habworks/Arb_Power_Booster/TestResults/Neg_20V_Inrush_And_Discharge/Discharge.png

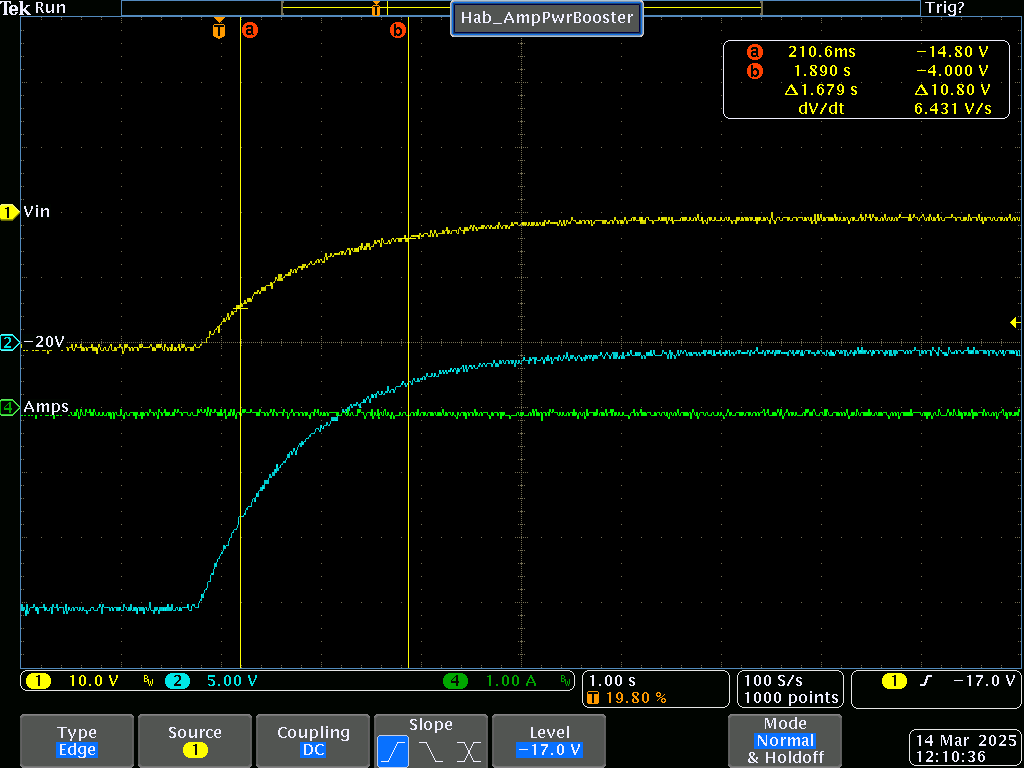
TestResults/Neg_20V_Inrush_And_Discharge/Discharge.png
