habworks/Arb_Power_Booster/TestResults/Neg_20V_Inrush_And_Discharge/Neg_20V_Inrush.png

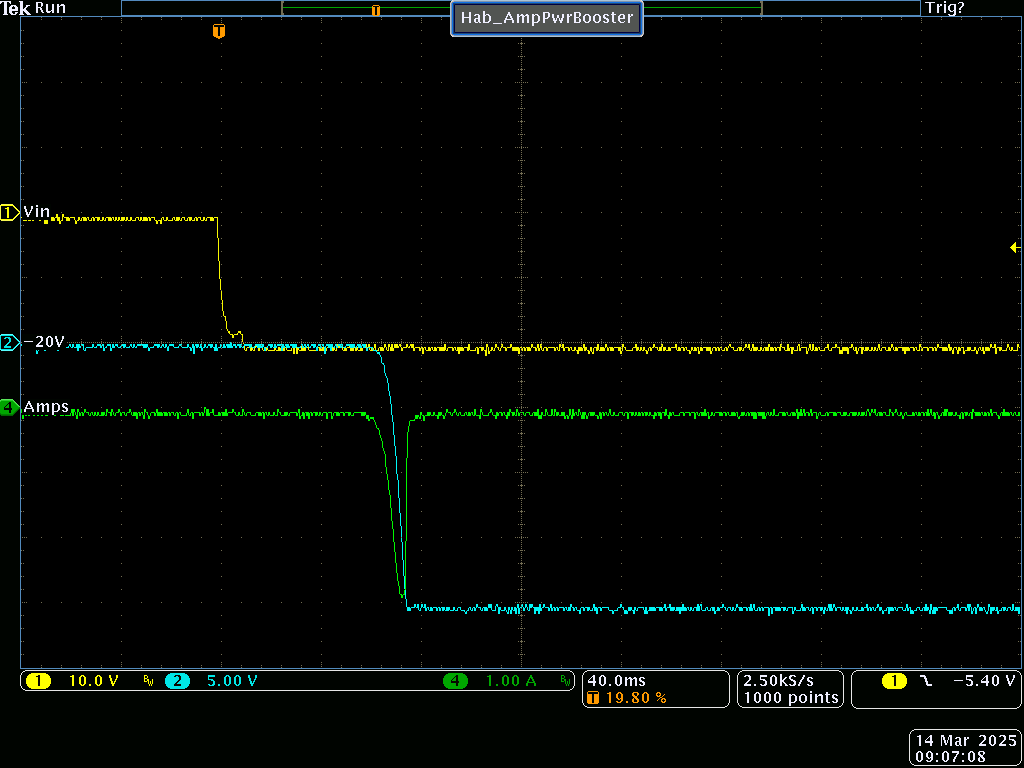
TestResults/Neg_20V_Inrush_And_Discharge/Neg_20V_Inrush.png
