habworks/Arb_Power_Booster/Simulate/Absolute_Value.asc

D1: diode; 1N4148
D2: diode; 1N4148
R1: res; 5K
R2: res; 10K
R3: res; 10K
R4: res; 10K
R5: res; 10K
R6: res; 10K
R7: res; 3K
R8: res; 4.99K
R9: res; 2.49K
U1: TLV9302
U3: TLV9302
V1: voltage; 15
V2: voltage; -15
V3: voltage; 10
Named nets: 0, VDD, VEE, VO, VIN, VO/2
.tran .010
