habworks/Arb_Power_Booster/Simulate/Current Amp-IC-Form-Single.asc

C1: cap; 300µF
C2: cap; .01µF
R1: res; 5
R2: res; 10
R3: res; .0065
R7: res; 10K
U1: OPA549
V1: voltage; -15V
V2: voltage; 15V
V3: voltage; SINE(9.5 .5 800 .001 0 0 10)
V4: voltage; 10
Named nets: 0, VS+, -VS, VIN, VO
.tran .003
