habworks/Arb_Power_Booster/Simulate/Current Amp-IC-Form-Dual.asc

C1: cap; 100µF
C2: cap; .01µF
R1: res; 3
R2: res; 10
R3: res; .1
R4: res; .1
R5: res; .001
R6: res; .001
R7: res; 10K
U1: OPA549
U2: OPA549
V1: voltage; -15V
V2: voltage; 15V
V3: voltage; SINE(10 1 5K .001 0 0 10)
Named nets: 0, VS+, -VS, VIN, VO
.tran .003
