habworks/Arb_Power_Booster/Simulate/NOT_USED_Current Amp-PowerAmp.asc

C1: cap; 100µ
D1: diode; 1N4148
D2: diode; 1N4148
D3: diode; 1N4148
Q1: npn; SST4401
Q2: pnp; SST4403
Q3: pnp; SST4403
Q4: npn; 2SCR582D3
Q5: npn; 2SCR582D3
Q6: npn; 2SCR582D3
Q7: npn; SST4401
Q8: npn; 2SCR582D3
R1: res; 500
R2: res; 500
R3: res; .2
R4: res; .2
R5: res; 1K
R6: res; 3.3
R7: res; 10
R8: res; 1K
R9: res; 10K
R10: res; 10K
R11: res; .2
R12: res; .2
U1: TLV9351
V1: voltage; 15
V2: voltage; -15
V3: voltage; SINE(10 1 5k 1m 0 0 10)
V4: voltage; 3.3
Named nets: 0, VCC, VEE, VO, VI, VT, VB
.tran 10m
