habworks/Arb_Power_Booster/Simulate/Current Amplifier-1_REV_21.asc

CL: cap; 300µ
D7: schottky; 1N5817
D8: schottky; 1N5817
Q1: npn; 2SCR582D3
Q2: npn; 2N4401
Q3: pnp; DJT4030P
Q4: pnp; 2SAR582D3
Q5: npn; 2N4401
Q6: pnp; MMBT4403
Q7: pnp; 2SAR582D3
Q8: npn; 2N4401
Q9: pnp; 2SAR582D3
Q10: pnp; MMBT4403
Q11: npn; 2SCR582D3
Q12: pnp; MMBT4403
Q13: npn; 2SCR582D3
Q14: npn; 2N4401
Q15: npn; DJT4031N
Q16: pnp; 2SAR582D3
Q17: pnp; MMBT4403
Q18: npn; 2SCR582D3
R1: res; 200
R2: res; 510
R3: res; .1
R4: res; .1
R5: res; .1
R6: res; .1
R7: res; .1
R8: res; .1
R9: res; .1
R10: res; .1
R11: res; .01
R12: res; .01
R13: res; 10K
R14: res; 500
RL: res; 3
U1: TLV9351
V1: voltage; 16
V2: voltage; -16
V3: voltage; SINE(10 2 5K .0005 0 0 10); AC 15
V4: voltage; 15
Named nets: VCC, VEE, 0, VO, VIN, VB1, VB2
.tran 3m
;ac dec 3m 10 10K
Note emitter resistance of R1 is less than R2 because it was found if they were even the
negative output voltage swing would be less than the positive output swing - This provides more 
available base current for amplification.
Full test condition is input of 10KHz at sine wave of +/-15V peak to peak.  This will be unrealistic
in a real environment, but the circuit can support it with some loss of amplitude (hence BW).
.MODEL DJT4030P PNP (IS=5.5e-13 NF=1 ISE=1.3e-13 NE=1.5 BF=360 VAF=36 IKF=8 ISC=1.1e-13 NC=1.28 BR=55 VAR=6.6 IKR=1.4 RE=9e-3 RB=300e-3 RC=9e-3 CJE=380e-12 VJE=0.7 MJE=0.4 CJC=111e-12 VJC=0.4 MJC=0.35 TF=8.5e-10 TR=3.7e-9 XTB=1.6 QUASIMOD=1 RCO=0.24 GAMMA=6e-10)
.MODEL DJT4031N NPN (IS=1e-14 BF=200 VAF=100 IKF=0.3 XTB=1.5 BR=5 CJC=10pF CJE=20pF TF=0.5ns TR=10ns)
