habworks/Arb_Power_Booster/Simulate/Current_Inrush_Limiter.asc

C1: cap; 10µ
C2: cap; 1000µ
C3: cap; 10µ
C4: cap; 1000µ
R1: res; 20K
R2: res; 58K
R3: res; 10K
R4: res; 20K
R5: res; 47K
R6: res; 10K
R7: res; 10K
R8: res; 1.236K
R9: res; 10K
R10: res; 1K
R11: res; 2.1K
U1: MMSZ5239BS
U2: DMP6050SPS-13
U3: MMSZ5239BS
U4: DMNH6042SPDQ-13
U5: DMNH6042SPDQ-13
U6: TLV9351
U7: BZT52C2V0S
U8: DMP6050SPS-13
V1: voltage; PULSE(0 20 10e-3 1e-5 1e-5 .5 1 2)
V2: voltage; PULSE(0 20 10e-3 1e-5 1e-5 .5 1 2)
V3: voltage; 20V
V4: voltage; -20V
V5: voltage; -30
Named nets: 0, VIN+, VO+, VG_A, VIN-, VO-, VG_B, VCC, VDD, VO
.tran 500E-3
Current inrush limiter. Works with zener or resistor R1 in circuit.  
 
When using Zener diode clamps the VGS so as not to exceed the max VGS of the PMOS
When using R1 the VGs limit is set by voltage divider of R1 and R2
 
In either case the C1 and R2 work to slow the turn on of the PMOSFET
Circuit also has the benefit of reverse voltage connection because of the PMOSFET body diode
OPTIONAL: You can cascade the MOSFET to reduce 
the total power (and in rush) they have to consume
OPTIONAL: You can cascade the MOSFET to reduce 
the total power (and in rush) they have to consume
