habworks/Arb_Power_Booster/Simulate/LeakageCurren_PosVoltageMonitor.asc

R1: res; 10K
R2: res; 1.24K
U3: MMSZ5226BS
V1: voltage; 20
Named nets: 0, Vo
.tran 1
