habworks/Arb_Power_Booster/Simulate/Signal_SSR_Switched_REV_2.asc

D1: LED
M1: nmos; 2N7002
R1: res; 10K
R2: res; 10K
R3: res; 1K
R4: res; 3K
R5: res; 8K
R6: res; 10K
U1: MMSZ5239BS
U2: IRLML5103TRPBF
U3: BZX84C3V6W-7-F
V1: voltage; 16
V2: voltage; -16
Named nets: 0, VDD, VSS
.tran 1
