habworks/Arb_Power_Booster/Simulate/NOT_USED_Add_Back_In_Vbe_Offset.asc

C1: cap; 1µF
Q1: npn; 2N3904
Q2: pnp; 2N3906
Q3: npn; 2N3904
Q4: pnp; 2N3906
R1: res; 20K
R2: res; 20K
R3: res; 5K
R4: res; 10K
R5: res; 10K
R6: res; 10K
R7: res; 10K
R8: res; 10K
R9: res; 10K
R10: res; 5K
R11: res; 10K
R12: res; 0
R13: res; 0
U1: TLV9351
U2: TLV9351
V1: voltage; 20V
V2: voltage; -20V
V3: voltage; SINE(10 5 1K .002 0 0 5)
Named nets: 0, V+, V-, VBE, VO, VI, SIG
.tran 9e-3
