habworks/Arb_Power_Booster/Simulate/Voltage_Monitor.asc

D1: diode; 1N4148
D2: diode; 1N4148
R1: res; 10K
R2: res; 1.236K
R7: res; 10K
R8: res; 1.236K
R9: res; 10K
R10: res; 1K
R11: res; 2.1K
U1: BZT52C2V0S
U2: BZX84C3V6W-7-F
U6: TLV9351
V1: voltage; 30V
V3: voltage; 20V
V4: voltage; -20V
V5: voltage; -30V
Named nets: 0, VCC, VDD, VO-, VO+
.tran .1
Creates a ration of 0.110 of input voltage - Max allowable +input of 30V to max output of 3.3V
Creates a ration of -0.110 of input voltage - Max allowable -input of -30V to max output of +3.3V
Supply rails +/-20V
See notes on circuit calculation
