habworks/Arb_Power_Booster/Simulate/NOT_USED_Current Amp-Adj_Bias-Servo-1.asc

C1: cap; 1µ
C2: cap; 300µ
C6: cap; 1µ
J1: njf; 2N5484
Q1: npn; 2SCR582D3
Q2: npn; 2SCR582D3
Q3: pnp; 2SAR582D3
Q4: pnp; 2SAR582D3
Q7: npn; 2SCR582D3
Q8: npn; 2N3904
Q9: npn; 2N3904
Q10: npn; 2N3904
Q11: pnp; 2N3906
Q12: pnp; 2N3906
Q13: pnp; 2N3906
Q14: pnp; 2SAR582D3
Q15: npn; 2N2219A
Q16: pnp; 2N2907
R1: res; .1
R2: res; .1
R3: res; 47K
R4: res; 1
R5: res; 1K
R6: res; 1
R7: res; 1
R8: res; 1
R9: res; 1K
R10: res; 1
R11: res; 1
R12: res; 39
R18: res; 62
R19: res; 150
R20: res; 150
R21: res; 62
R22: res; 68
R23: res; 68
R24: res; .1
R25: res; .1
R26: res; 1
R27: res; 1
R28: res; 100
R29: res; 3
R30: res; 100
R31: res; 100
R32: res; .1
R33: res; .1
R34: res; 100K
R35: res; 100K
U2: LT1368
V1: voltage; SINE(0 15 4.7K 1m 0 0 10)
V4: voltage; 20
V5: voltage; 20
V6: voltage; 15
V7: voltage; 15
Named nets: 0, +V, -V, +15V, -15V, VIN, VO
.tran 3m
