habworks/Arb_Power_Booster/Firmware/ArbPwrBooster_App/STM32CubeIDE/Application/User/App_Support/Src/PID_Controller.c

/******************************************************************************************************
 * @file 			PID_Controller.c
 * @brief			Proportional-Integral-Derivative (PID) controller functions
 * ****************************************************************************************************
 * @author original Hab Collector (habco)\n
 *
 * @version         See Main_Support.h: FW_MAJOR_REV, FW_MINOR_REV, FW_TEST_REV
 *
 * @param Development_Environment \n
 * Hardware:        <STM32F764G-DISCO> \n
 * IDE:             STMCubeIDE VER 1.17.0 \n
 * Compiler:        GCC \n
 * Editor Settings: 1 Tab = 4 Spaces, Recommended Courier New 11
 *
 * @note            The associated header file provides MACRO functions for IO control
 *
 *                  This is an embedded application
 *                  It will be necessary to consult the reference documents to fully understand the code
 *                  It is suggested that the documents be reviewed in the order shown.
 *                    Schematic: IMR-005-SCH
 *                    STM32F746G_DISCO
 *                    IMR Engineering
 *
 * @copyright       IMR Engineering, LLC
 ********************************************************************************************************/

#include "PID_Controller.h"
#include "Main_Support.h"
#include <stdlib.h>


/********************************************************************************************************
* @brief Init of a PID struct for use.  Allocate the memory for use with the PID, assign the gains and set
* the init conditions
*
* @author original: Hab Collector \n
*
* @note: This memory is allocated and should never be freed
*
* @param Kp: Proportional Gain
* @param Ki: Integral Gain
* @param Kd: Derivative Gain
* @param MaxStepValue: Digital Pot reset value in steps see MCP45HVX1 driver
*
* @return: Pointer to the PID Controller structure
*
* STEP 1: Allocate the memory
* STEP 2: Assign gain constants and init conditions
********************************************************************************************************/
Type_PID_Controller * Init_PID_Controller(float Kp, float Ki, float Kd, uint8_t MaxStepValue)
{
    // STEP 1: Allocate the memory
    Type_PID_Controller *PID = (Type_PID_Controller *)malloc(sizeof(Type_PID_Controller));
    if (PID == NULL)
        systemErrorHandler(__FILE__, __LINE__, 0, "Failed to allocate memory for PID");

    // STEP 2: Assign gain constants and init conditions
    PID->Enable = false;
    PID->ProportionalGain = Kp;
    PID->IntegralGain = Ki;
    PID->DerivativeGain = Kd;
    PID->PreviousError = 0;
    PID->Integral = 0;
    PID->Output = 0;
    PID->PotStep = 0;
    PID->MaxStepValue = MaxStepValue;

    return(PID);

} // END OF Init_PID_Controller



/********************************************************************************************************
* @brief Reseting of the PID values when not in use - By resetting the error when not in use, the error terms
* in particular the integral term does not grow unbounded.
*
* @author original: Hab Collector \n
*
* @param PID: PID Controller Handle
*
* STEP 1: PID_Reset
* ********************************************************************************************************/
void PID_Reset(Type_PID_Controller *PID_Controller)
{
    // STEP 1: PID_Reset
    PID_Controller->Enable = false;
    PID_Controller->Integral = 0;
    PID_Controller->PreviousError = 0;

} // END OF PID_Reset



/********************************************************************************************************
* @brief Update the digital pot to control the current set point.  The digital pot is a divider to the output
* signal.  When the current limit is surpassed, the digital pot is used to limit the output voltage.  By
* limiting the output voltage, the output current is reduced.  When the output voltage is reduced to the point
* the output current matches the current limit - this is in effect constant current mode.  The feedback loop
* encompasses the output current measure, the current limit, and the digital POT control.
*
* @author original: Hab Collector \n
*
* @note: This memory is allocated and should never be freed
*
* @param PID: PID Controller Handle
* @param MeasuredCurrent: Present current value
* @param CurrentLimit: current limit allowed
* @param DeltTime: Time between current samples
*
* @return: PID status
*
* STEP 1: Calculate the present error
* STEP 2: Calculate the Integral term
* STEP 3: Calculate the Derivative term
* STEP 4: Calculate the PID output (before conversion to digital pot units) by the sum of all errors
* STEP 5: Convert PID output to digital pot value
* STEP 6: Clamp PotValue within allowed range (0 to Total number of pot steps)
* STEP 7: Update digital pot step value - if step results in no attenuation reset the PID values
* ********************************************************************************************************/
Type_PID_Status PID_updateDigitalPot(Type_PID_Controller *PID, float MeasuredCurrent, float CurrentLimit, float DeltaTime)
{
    // STEP 1: Calculate the present error
    float PresentError = MeasuredCurrent - CurrentLimit;

    // STEP 2: Calculate the Integral term
    PID->Integral += PresentError * DeltaTime;

    // Optional: Integral anti-windup clamp (commented out, can be enabled if needed)
    // For now covered in step 7
//    if (PID->Integral > MaxIntegral)
//        PID->Integral = MaxIntegral;
//    else if (PID->Integral < 0.0f)
//        PID->Integral = 0.0f;

    // STEP 3: Calculate the Derivative term
    float Derivative = (PresentError - PID->PreviousError) / DeltaTime;
    PID->PreviousError = PresentError;

    // STEP 4: Calculate the PID output (before conversion to digital pot units) by the sum of all errors
    PID->Output = (PID->ProportionalGain * PresentError)
                + (PID->IntegralGain * PID->Integral)
                + (PID->DerivativeGain * Derivative);

    // STEP 5: Convert PID output to digital pot value
    int PotValue = (int)(PID->Output + 0.5f);   // Round to nearest integer
    PotValue = PID->MaxStepValue - PotValue;    // Must Invert Pot value: 0 = max attenuation, 255 = no attenuation

    // STEP 6: Clamp PotValue within allowed range (0 to Total number of pot steps)
    if (PotValue < 0)
    {
        PotValue = 0;
    }
    else if (PotValue > PID->MaxStepValue)
    {
        PotValue = PID->MaxStepValue;
    }
    // TODO: Hab test this MACRO - if good use it
    // PotValue = MIN_MAX_CLAMP(PotValue, 0, PID->MaxStepValue);

    // STEP 7: Update digital pot step value - if step results in no attenuation reset the PID values
    PID->PotStep = (uint8_t)PotValue;
    PID->Enable = (PID->PotStep == PID->MaxStepValue)? false:true;
    if (!PID->Enable)
        PID_Reset(PID);

    return(PID_UPDATE);

} // END OF PID_updateDigitalPot
