habworks/Arb_Power_Booster/Firmware/ArbPwrBooster_App/STM32CubeIDE/Application/User/App_Support/Src/ADC_Support.c

/** ****************************************************************************************************
 * @file            ADC_Support.c
 * @brief           A collection of functions relevant to the ADC peripheral channels and their conversions
 * ****************************************************************************************************
 * @author original Hab Collector (habco)\n
 *
 * @version         See Main_Support.h: FW_MAJOR_REV, FW_MINOR_REV, FW_TEST_REV
 *
 * @param Development_Environment \n
 * Hardware:        <STM32F764G-DISCO> \n
 * IDE:             STMCubeIDE VER 1.17.0 \n
 * Compiler:        GCC \n
 * Editor Settings: 1 Tab = 4 Spaces, Recommended Courier New 11
 *
 * @note            The associated header file provides MACRO functions for IO control
 *
 *                  This is an embedded application
 *                  It will be necessary to consult the reference documents to fully understand the code
 *                  It is suggested that the documents be reviewed in the order shown.
 *                    Schematic: IMR-005-SCH
 *                    STM32F746G_DISCO
 *                    IMR Engineering
 *
 * @copyright       IMR Engineering, LLC
 ********************************************************************************************************/

#include "ADC_Support.h"
#include "Main_Support.h"
#include "IO_Support.h"
#include "Terminal_Emulator_Support.h"
#include "MCP45HVX1_Driver.h"
#include "RMS_Calculate.h"
#include "PID_Controller.h"
#include "stm32f7xx_hal_adc.h"
#include "cmsis_os2.h"
#include <string.h>
#include <stdlib.h>
#include <stdio.h>
#include <math.h>


extern ADC_HandleTypeDef hadc1;
extern ADC_HandleTypeDef hadc3;

// Global
uint16_t ADC1_CountValue[ADC1_NUMBER_OF_CHANNELS];
uint16_t ADC3_CountValue[ADC3_NUMBER_OF_CHANNELS];
static double System_ADC_Reference = ADC_REFERENCE_VOLTAGE;     // Init condition - it will be updated later in calculation of ADC1 3V3

// Static Function Declarations
static Type_16b_FIFO *Init_FIFO_Buffer(uint16_t *Buffer, uint8_t BufferLength, uint16_t InitLoadValue);
static void writeTo_FIFO_Buffer(Type_16b_FIFO *Buffer, uint16_t Value);
static double calculateSystem_3V3(void);
static double calculateSystemTemp(void);
static double calculateSystemSupply(Type_16b_FIFO *FIFO_SupplyRail);
static void calculateChannelCurrent(double ADC_AmpMonitorCount, Type_16b_FIFO *FIFO_AmpMon, Type_ChannelConfig *Channel, Type_RMS *RMS_AmpMon);
static void calculateChannelVoltage(double ADC_VoltMonitorCount, Type_16b_FIFO *FIFO_VoltMon, Type_ChannelConfig *Channel, Type_RMS *RMS_VoltMon);

// Static FIFO Declarations
// System 3V3
static uint16_t BufferSystem_3V3[SYSTEM_3V3_BUFFER_SIZE] = {0x0000};
static Type_16b_FIFO *FIFO_System_3V3;
// System Temperature
static uint16_t BufferSystemTemp[SYSTEM_TEMP_BUFFER_SIZE] = {0x0000};
static Type_16b_FIFO *FIFO_SystemTemp;
// Positive VS Supply Rail Monitor
static uint16_t Buffer_PVS_Supply[SYSTEM_PVS_BUFFER_SIZE] = {0x0000};
static Type_16b_FIFO *FIFO_PVS_Supply;
// Negative VS Supply Rail Monitor
static uint16_t Buffer_NVS_Supply[SYSTEM_NVS_BUFFER_SIZE] = {0x0000};
static Type_16b_FIFO *FIFO_NVS_Supply;
// CH1 Current Monitor
static uint16_t Buffer_CH1_AmpMon[CH1_AMP_MON_BUFFER_SIZE] = {0x0000};
static Type_16b_FIFO *FIFO_CH1_AmpMon;
// CH2 Current Monitor
static uint16_t Buffer_CH2_AmpMon[CH2_AMP_MON_BUFFER_SIZE] = {0x0000};
static Type_16b_FIFO *FIFO_CH2_AmpMon;
// CH1 Current Monitor
static uint16_t Buffer_CH1_VoltMon[CH1_VOLT_MON_BUFFER_SIZE] = {0x0000};
static Type_16b_FIFO *FIFO_CH1_VoltMon;
// CH2 Current Monitor
static uint16_t Buffer_CH2_VoltMon[CH2_VOLT_MON_BUFFER_SIZE] = {0x0000};
static Type_16b_FIFO *FIFO_CH2_VoltMon;

// Static RMS Struct Declarations
static float CH1_AmpMonBuffer[RMS_WINDOW_SIZE];
static Type_RMS *RMS_CH1_AmpMon;
static float CH2_AmpMonBuffer[RMS_WINDOW_SIZE];
static Type_RMS *RMS_CH2_AmpMon;
static float CH1_VoltMonBuffer[RMS_WINDOW_SIZE];
static Type_RMS *RMS_CH1_VoltMon;
static float CH2_VoltMonBuffer[RMS_WINDOW_SIZE];
static Type_RMS *RMS_CH2_VoltMon;

// Static PID Controller Declarations
//static Type_PID_Controller *PID_CH1_DigitalPot;


/********************************************************************************************************
* @brief Init the ADC for ADC1 (2 channels) and ADC3 (3 channels).
* ADC1 handles:
*    Temperature
*    3.3V measurement
* ADC3 handles:
*    -VS Supply Rail
*    +VS Supply Rail
*    CH1 Current Monitor
*    CH2 Current Monitor
*    CH1 Voltage Monitor
*    CH2 Voltage Monitor
*
* @author original: Hab Collector \n
*
* @note: ADC1 is set in DMA single shot conversion mode - software start required for new conversion
* @note: ADC3 is set in DMA continuous conversion mode - continuous non-stop conversions once started
* @note: See the ADC DMA callback HAL_ADC_ConvCpltCallback
* @note: The STM32F series makes no provision for a calibration as it is trimmed by the factory
* @note: See function ADC13_StartConversion() - which actually starts the conversion
* @note: See also ArbPwrBooster member Ready
*
* STEP 1: Enable Internal reference and temperature measure
* STEP 2: Init FIFO Buffers for use with ADC1: Micro-Temp Sensor, System 3.3V
* STEP 3: Init FIFO Buffers for use with ADC3: ±VS rail, CH1 & CH2 Amp Monitor
* STEP 4: Init RMS structures
* STEP 5: Init PID structures
********************************************************************************************************/
void Init_ADC_Hardware(void)
{
    // STEP 1: Enable Internal reference and temperature measure
    ADC->CCR |= ADC_CCR_TSVREFE_Msk;

    // STEP 2: Init FIFO Buffers for use with ADC1: Micro-Temp Sensor, System 3.3V
    FIFO_SystemTemp = Init_FIFO_Buffer(BufferSystemTemp, SYSTEM_TEMP_BUFFER_SIZE, 0);
    FIFO_System_3V3 = Init_FIFO_Buffer(BufferSystem_3V3, SYSTEM_3V3_BUFFER_SIZE, ADC_REF_VOLTAGE_COUNT);

    // STEP 3: Init FIFO Buffers for use with ADC3: ±VS rail, CH1 & CH2 Amp Monitor
    FIFO_NVS_Supply = Init_FIFO_Buffer(Buffer_NVS_Supply, SYSTEM_NVS_BUFFER_SIZE, 0);
    FIFO_PVS_Supply = Init_FIFO_Buffer(Buffer_PVS_Supply, SYSTEM_PVS_BUFFER_SIZE, 0);
    FIFO_CH1_AmpMon = Init_FIFO_Buffer(Buffer_CH1_AmpMon, CH1_AMP_MON_BUFFER_SIZE, 0);
    FIFO_CH2_AmpMon = Init_FIFO_Buffer(Buffer_CH2_AmpMon, CH2_AMP_MON_BUFFER_SIZE, 0);
    FIFO_CH1_VoltMon = Init_FIFO_Buffer(Buffer_CH1_VoltMon, CH1_VOLT_MON_BUFFER_SIZE, 0);
    FIFO_CH2_VoltMon = Init_FIFO_Buffer(Buffer_CH2_VoltMon, CH2_VOLT_MON_BUFFER_SIZE, 0);

    // STEP 4: Init RMS structures
    RMS_CH1_AmpMon = Init_RMS_Class(CH1_AmpMonBuffer, RMS_WINDOW_SIZE);
    RMS_CH2_AmpMon = Init_RMS_Class(CH2_AmpMonBuffer, RMS_WINDOW_SIZE);
    RMS_CH1_VoltMon = Init_RMS_Class(CH1_VoltMonBuffer, RMS_WINDOW_SIZE);
    RMS_CH2_VoltMon = Init_RMS_Class(CH2_VoltMonBuffer, RMS_WINDOW_SIZE);

    // STEP 5: Init PID structures
    ArbPwrBooster.CH1.PID = Init_PID_Controller(PID_Pk, PID_Pi, PID_Pd, MCP45HVX1_POT_FULL_RESOLUTION);
    ArbPwrBooster.CH2.PID = Init_PID_Controller(PID_Pk, PID_Pi, PID_Pd, MCP45HVX1_POT_FULL_RESOLUTION);

} // END OF Init_ADC_Hardware



/********************************************************************************************************
* @brief Start Conversions for both ADC1 and ADC3.  Note this function should be call only once as part of
* the start up process.  Though ADC1 is configured in single shot mode and the start can be called on the
* completion of every ADC1 conversion, ADC3 is configured in circular mode and does not (should not) be called
* repeatedly as the conversions will automatically restart.
*
* @author original: Hab Collector \n
*
* @note: ADC1 is configured in single shot mode and its conversion rate is based on the rate at which it is called
* @note: ADC3 is configured in circular mode and will automatically restart the conversions
*
* STEP 1: Start ADC 1 & ADC 3 conversion all channels
********************************************************************************************************/
void ADC13_StartConversion(void)
{
    HAL_StatusTypeDef ADC_InitStatus = HAL_OK;

    // STEP 1: Start ADC 1 & ADC 3 conversion all channels
    ADC_InitStatus |= HAL_ADC_Start_DMA(&hadc1, (uint32_t *)ADC1_CountValue, ADC1_NUMBER_OF_CHANNELS);
    ADC_InitStatus |= HAL_ADC_Start_DMA(&hadc3, (uint32_t *)ADC3_CountValue, ADC3_NUMBER_OF_CHANNELS);
    if (ADC_InitStatus != HAL_OK)
        systemErrorHandler(__FILE__, __LINE__, 0, "Failed to init ADC peripheral");

} // END OF ADC13_StartConversion



/********************************************************************************************************
* @brief Redefinition of the weak callback function for ADC conversion complete.  ADC1 and ADC3 values
* have been acquired this function updates the corresponding FIFO buffers and calls a unique function that
* performs the channel conversion.  Within ADC3 an attempt is made to make a more accurate (calibrated) measure
* An ADC offset error and gain error are channel specific measurements that are made to improve the overall
* accuracy of the ADC count reading.  The offset error is measure in ADC counts when the input to the ADC channel
* is at GND - ideally it should be 0, but if not, this is how many counts the ADC is offset by and therefore
* must be subtracted out.  The gain error relates more to quantization effects of the ADC.  It is measured at the
* highest ADC input possible (System Reference Voltage if possible, but certainly as large as you can get)
* and its value should ideally be 4096 (12b ADC) (if input is System Reference Voltage) or the expected calculated
* value. The Gain Error (GE) is calculated as Measured / Expected - no gain error would be a value of 1.0
*
* The counter var VS_UpdateCount was added.  This callback routine really runs for too long.  Without the
* use of VS_UpdateCount the TouchGFX will crash.  VS_UpdateCount minimize the time time spent in this callback
* by mostly not updating the VS supply rails - which in fact will not be changing by much, nor is there an RMS
* associated calculation - just an average.  A value of 1000 is used for the delay but as little as 10 worked.
* It is balance between update speed of the VS supply rail mean and the smoothness of the TouchGFX operation.
*
* ADC1 handles:
*    Temperature
*    3.3V measurement
* ADC3 handles:
*    -VS Supply Rail
*    +VS Supply Rail
*    CH1 Current Monitor
*    CH2 Current Monitor
*    CH1 Voltage Monitor
*    CH2 Voltage Monitor
*
* ADC1 Configuration
* RANK  ADC_CH  Port    Cycles  Net Name
* 1     Temp    NA      480     NA - Internal to IC
* 2     Vref    NA      480     NA - Internal to IC
*
* ADC3 Configuration:
* RANK  ADC_CH  Port    Cycles  Net Name
* 1     IN6     PF8     144     -VS_MON
* 2     IN7     PF9     144     +VS-MON
* 3     IN0     PA0     144     IO_MON_1
* 4     IN8     PF10    144     IO_MON_2
* 5     IN4     PF6     144     VI_MON_2
* 6     IN5     PF7     144     VI_MON_1
*
* ADC uses PCLK2 (108MHz) with a divisor of 8
*
* @author original: Hab Collector \n
*
* @note: This is redefinition - this function is define weak in the HAL but implemented here
* @note: The Rate toggle outputs are used to verify ADC conversion rate.  Conversion rate is calculated as:
* PCLK2 / ADC_Clock_Presclar * Total Conversion Cycles For All ADC_Channels
* @note: ADC3 conversion time = 64.00us or 15.625KHz (This is the sampling frequency)
* @note: ADC1 conversion time = 71.11us but the sample rate is governed by mainUpdateTaskActions() / GUI_UPDATE_RATE
* @note: As the sampling frequency is 15.63KHz the max frequency of the input signal (nyquist) 7.813KHz
* @note: The sampling frequency was limited by the Touch GFX - As this computation must take place periodically and
* outside of a task, faster sampling frequencies (for example 20KHz) could not be sustained without crashing the TouchGFX
* That said there is some room to possibly tweak this a little higher.  If only the channel current is being
* calculated for RMS you can definitely run at 20KHz sampling.  However the 15.63KHz sample is adjusted for
* both channels current and voltage monitoring RMS.
*
* @param hadc: Pointer to the ADC handler (ADC1 or ADC3)
*
* STEP 1: ADC1 Conversions: Micro-Temp Sensor, System 3.3V
* STEP 2: ADC3 Conversions: ±VS rail, CH1 & CH2 Amp Monitor
********************************************************************************************************/
void HAL_ADC_ConvCpltCallback(ADC_HandleTypeDef *hadc)
{
    static uint16_t VS_UpdateCount = 0;

    // STEP 1: ADC1 Conversions: Micro-Temp Sensor, System 3.3V
    if (hadc == &hadc1)
    {
        // System Temperature: See section 15.10 of STM32F746 Reference Manual (RM0385)
        writeTo_FIFO_Buffer(FIFO_SystemTemp, ADC1_CountValue[RANK_1]);
        ArbPwrBooster.SystemMeasure.TempDegreeC = calculateSystemTemp();
        // System 3.3V
        writeTo_FIFO_Buffer(FIFO_System_3V3, ADC1_CountValue[RANK_2]);
        System_ADC_Reference = calculateSystem_3V3();
        ArbPwrBooster.SystemMeasure.VDD_VDREF = System_ADC_Reference;
        // Stop the one shot ADC - it must be started
        HAL_ADC_Stop_DMA(&hadc1);
        // Toggle at the end of conversion - for testing: ADC1 actual conversion rate versus calculated - using here ADC3_C_RATE_TOGGLE() must comment out its use in step 2
        // ADC3_C_RATE_TOGGLE();
    }

    // STEP 2: ADC3 Conversions: ±VS rail, CH1 & CH2 Amp Monitor, CH1 & CH2 Volt Monitor
    if (hadc == &hadc3)
    {
        double ADC3_ErrorCompensatedCount;
        VS_UpdateCount++;
        if (VS_UpdateCount == 1000) // 1000 Value found by trial but it worked with as little as 10
        {
            // -VS Supply Rail
            ADC3_ErrorCompensatedCount = ((double)ADC3_CountValue[RANK_1] - ADC_NVS_OFFSET_ERROR) / ADC_NVS_GAIN_ERROR;
            writeTo_FIFO_Buffer(FIFO_NVS_Supply, ADC3_ErrorCompensatedCount);
            ArbPwrBooster.SystemMeasure.Negative_VS = calculateSystemSupply(FIFO_NVS_Supply) * -1.0;
            // +VS Supply Rail
            ADC3_ErrorCompensatedCount = ((double)ADC3_CountValue[RANK_2] - ADC_PVS_OFFSET_ERROR) / ADC_PVS_GAIN_ERROR;
            writeTo_FIFO_Buffer(FIFO_PVS_Supply, ADC3_ErrorCompensatedCount);
            ArbPwrBooster.SystemMeasure.Positive_VS = calculateSystemSupply(FIFO_PVS_Supply);
            VS_UpdateCount = 0;
        }
        // Current Monitor CH1
        ADC3_ErrorCompensatedCount = ((double)ADC3_CountValue[RANK_3] - ADC_IMON1_OFFSET_ERROR) / ADC_IMON1_GAIN_ERROR;
        writeTo_FIFO_Buffer(FIFO_CH1_AmpMon, ADC3_ErrorCompensatedCount);
        calculateChannelCurrent(ADC3_ErrorCompensatedCount, FIFO_CH1_AmpMon, &ArbPwrBooster.CH1, RMS_CH1_AmpMon);
        // Current Monitor CH2
        ADC3_ErrorCompensatedCount = ((double)ADC3_CountValue[RANK_4] - ADC_IMON2_OFFSET_ERROR) / ADC_IMON2_GAIN_ERROR;
        writeTo_FIFO_Buffer(FIFO_CH2_AmpMon, ADC3_ErrorCompensatedCount);
        calculateChannelCurrent(ADC3_ErrorCompensatedCount, FIFO_CH2_AmpMon, &ArbPwrBooster.CH2, RMS_CH2_AmpMon);
        // Voltage Monitor CH1
        ADC3_ErrorCompensatedCount = ((double)ADC3_CountValue[RANK_6] - ADC_VMON1_OFFSET_ERROR) / ADC_VMON1_GAIN_ERROR;
        writeTo_FIFO_Buffer(FIFO_CH1_VoltMon, ADC3_ErrorCompensatedCount);
        calculateChannelVoltage(ADC3_ErrorCompensatedCount, FIFO_CH1_VoltMon, &ArbPwrBooster.CH1, RMS_CH1_VoltMon);
        // Voltage Monitor CH2
        ADC3_ErrorCompensatedCount = ((double)ADC3_CountValue[RANK_5] - ADC_VMON2_OFFSET_ERROR) / ADC_VMON2_GAIN_ERROR;
        writeTo_FIFO_Buffer(FIFO_CH2_VoltMon, ADC3_ErrorCompensatedCount);
        calculateChannelVoltage(ADC3_ErrorCompensatedCount, FIFO_CH2_VoltMon, &ArbPwrBooster.CH2, RMS_CH2_VoltMon);
        // Toggle at the end of conversion - for testing: ADC3 actual conversion rate versus calculated
        ADC3_C_RATE_TOGGLE();
    }

} // END OF HAL_ADC_ConvCpltCallback



/********************************************************************************************************
* @brief Init of a FIFO buffer for use.  The base memory location for the buffer is cleared and memory for
* type is allocated.  The buffer is init with the write position at index 0
*
* @author original: Hab Collector \n
*
* @note: The passed buffer must be of type uint16_t
* @note: This memory is allocated and should never be freed
* @note: Buffers used for the collection of data used in a rolling average
*
* @param Buffer: Pointer to memory that will hold the buffer
* @param BufferLength: The total number of uint16_t
* @param InitLoadValue: Init value of the buffer
*
* @return: Pointer to the FIFO buffer structure
*
* STEP 1: Set the buffer values to 0 and allocate memory for the struct pointer
* STEP 2: Assign buffer pointer, length and set write location to buffer index
* STEP 3: Load the buffer with the init value
********************************************************************************************************/
static Type_16b_FIFO *Init_FIFO_Buffer(uint16_t *Buffer, uint8_t BufferLength, uint16_t InitLoadValue)
{
    // STEP 1: Set the buffer values to 0 and allocate memory for the struct pointer
    memset(Buffer, 0x00, (sizeof(uint16_t) * BufferLength));
    Type_16b_FIFO *FIFO_16Bit = (Type_16b_FIFO *)malloc(sizeof(Type_16b_FIFO));
    if (FIFO_16Bit == NULL)
        systemErrorHandler(__FILE__, __LINE__, 0, "Failed to allocate memory for FIFO");

    // STEP 2: Assign buffer pointer, length and set write location to buffer index
    FIFO_16Bit->Buffer = Buffer;
    FIFO_16Bit->Depth = BufferLength;
    FIFO_16Bit->WritePointer = &Buffer[0];
    FIFO_16Bit->Sum = 0;
    FIFO_16Bit->FirstOverFlow = false;

    // STEP 3: Load the buffer with the init value
    for (uint8_t Index = 0; Index < BufferLength; Index++)
    {
        writeTo_FIFO_Buffer(FIFO_16Bit, InitLoadValue);
    }

    return(FIFO_16Bit);

} // END OF Init_FIFO_Buffer



/********************************************************************************************************
* @brief Write a value to the FIFO buffer.  The write pointer is advance automatically.  The write pointer
* will loop back to the index to avoid memory leak.  A sum is calculated by means of adding the newest and
* removing the previous value - quicker than incrementally summing buffer values externally.
*
* @author original: Hab Collector \n
*
* @note: See Init_FIFO_Buffer function for additional details
* @note: Sum and depth members can be used for a quick external calculation of mean
*
* @param FIFO: Pointer to the 16b FIFO
* @param NewValue: Value to be written into FIFO - replaces oldest value
*
* STEP 1: Calculate buffer sum
* STEP 2: Write Value to the present location
* STEP 3: Advance write pointer to next address - loop back when end of write locations reached
********************************************************************************************************/
static void writeTo_FIFO_Buffer(Type_16b_FIFO *FIFO, uint16_t NewValue)
{
    // STEP 1: Calculate buffer sum
    if (!FIFO->FirstOverFlow)
    {
        FIFO->Sum = FIFO->Sum + NewValue;
    }
    else
    {
        uint16_t LastValue = *FIFO->WritePointer;
        FIFO->Sum = FIFO->Sum + NewValue;
        FIFO->Sum = FIFO->Sum - LastValue;
    }

    // STEP 2: Write Value to the present location
    *FIFO->WritePointer = NewValue;

    // STEP 3: Advance write pointer to next address - loop back when end of write locations reached
    uint16_t *NewWritePointer = FIFO->WritePointer + 1;
    if (NewWritePointer >= (FIFO->Buffer + FIFO->Depth))
    {
        FIFO->WritePointer = FIFO->Buffer;
        FIFO->FirstOverFlow = true;
    }
    else
        FIFO->WritePointer = NewWritePointer;

} // END OF writeTo_FIFO_Buffer



/********************************************************************************************************
* @brief Calculate the SYSTEM 3V3 voltage using the internal reference.  Formula is:
*    VDD = (Factory_ReferenceCalibration * 3.3) / ADC_VrefInt
* The ADC_VrefInt is mean value of a FIFO buffer which is used to establish a filtered result
*
* @author original: Hab Collector \n
*
* @note: For the STM32F746G-DISCO The Vref and VDD are the same
* @note: SYSTEM refers to quantities that impact the entire device - CHANNEL impacts on CH1 or CH2
*
* @return System VREF value the actual value we do not presume it is 3.3V
*
* STEP 1: Write Value to the present location
* STEP 2: Advance write pointer to next address - loop back when end of write locations reached
********************************************************************************************************/
static double calculateSystem_3V3(void)
{
    // STEP 1: Calculate the mean of the ADC 3V3 counts
    double Mean_3V3_Count = 0.0;
    Mean_3V3_Count = (double)((double)FIFO_System_3V3->Sum / FIFO_System_3V3->Depth);

    // STEP 2: Using the mean value calculate the System 3V3
    uint16_t VRefInternalCal = *VREFINT_CAL_ADDR;
    double System_3V3 = (VRefInternalCal * ADC_REFERENCE_VOLTAGE) / Mean_3V3_Count;
    return(System_3V3);

} // END OF calculateSystem_3V3



/********************************************************************************************************
* @brief Calculate the SYSTEM temperature.  The formula is taken from See section 15.10 of STM32F746 Reference
* Manual (RM0385).  Makes uses of the filtered value for Vref (System_ADC_Reference).
*
* @author original: Hab Collector \n
*
* @note: For the STM32F746G-DISCO The Vref and VDD are the same
* @note: SYSTEM refers to quantities that impact the entire device - CHANNEL impacts on CH1 or CH2
* @note: According to the datasheet this is not going to be a very accurate absolute measure because of the
* temperature offset.  However it should be very good at making relative measurements to ±1.5C°.
*
* @return System Temperature in °C as measured by the STM32F746 uC.
*
* STEP 1: Calculate the mean of the ADC Temperature counts
* STEP 2: Using the mean value calculate the System Temperature in °C
********************************************************************************************************/
static double calculateSystemTemp(void)
{
    // STEP 1: Calculate the mean of the ADC Temperature counts
    double MeanTempCount = 0.0;
    MeanTempCount = (double)((double)FIFO_SystemTemp->Sum / FIFO_SystemTemp->Depth);

    // STEP 2: Using the mean value calculate the System Temperature in °C
    double VoltageTempSensor = (MeanTempCount * System_ADC_Reference) / ADC_12BIT_FULL_COUNT;
    double Temperature = ((VoltageTempSensor - VOLTAGE_AT_25C) / AVG_TEMP_SLOPE) + TEMP_25C;
    return(Temperature);

} // END OF calculateSystemTemp



/********************************************************************************************************
* @brief Calculates the SYSTEM ±VS supply rail voltage.  The negative supply rail is inverted externally so it is
* read here as a positive value.  If the calling function is passing the negative supply rail FIFO it must
* also multiply the return value by -1.
*
* @author original: Hab Collector \n
*
* @note: External divider ratio of .110 (30V to 3.3V)
* @note: Divider ratio for ±VS is the same
* @note: Nominal supply voltage is 15V
* @note: SYSTEM refers to quantities that impact the entire device - CHANNEL impacts on CH1 or CH2
*
* @param FIFO_SupplyRail FIFO struct associated with specific supply voltage channel
* @param InputOffsetError: ADC Input offset error as measured at ADC input for +VS or -VS
* @param GainError: ADC Gain error measured at the max value of VS as a ratio of expected counts / actual counts
*
* @return As a positive number only the supply rail voltage
*
* STEP 1: Calculate the mean of the ADC Supply rail counts
* STEP 2: Using the mean value calculate supply rail according to input divider ratio
********************************************************************************************************/
static double calculateSystemSupply(Type_16b_FIFO *FIFO_SupplyRail)
{
    // STEP 1: Calculate the mean of the ADC Supply rail counts
    double MeanSupplyRailCount = (double)((double)FIFO_SupplyRail->Sum / FIFO_SupplyRail->Depth);

    // STEP 2: Using the mean value calculate supply rail according to input divider ratio
    double SupplyRailVoltage = MeanSupplyRailCount * LSB_12BIT_VALUE * System_ADC_Reference * SYSTEM_VS_DIVIDER;
    return(SupplyRailVoltage);

} // END OF calculateSystemSupply



/********************************************************************************************************
* @brief Calculates the CHANNEL mean, max, min and RMS current.  The RMS value is used in the PID control
* of Constant Current Mode at the point of measure.  As such its accuracy needs to be right.  The RMS is
* a true RMS it is calculated by the formula RMS = sqrt(1/N * Sum(x*x)).
*
* @author original: Hab Collector \n
*
* @note: SYSTEM refers to quantities that impact the entire device - CHANNEL impacts on CH1 or CH2
*
* @param ADC_AmpMonitorCount: ADC Count from ADC channel for the specific current monitor
* @param FIFO_AmpMon: FIFO structure associated with the specific Amp Monitor channel
* @param Channel: ArbPwrBooster current measure struct associated with the specific channel
* @param RMS_AmpMon: Associated RMS structure
*
* STEP 1: Calculate the mean of the Current Monitor
* STEP 2: Calculate the instantaneous current
* STEP 3: Update Min Max current or reset min if so desired
* STEP 4: Calculate the RMS current
********************************************************************************************************/
static void calculateChannelCurrent(double ADC_AmpMonitorCount, Type_16b_FIFO *FIFO_AmpMon, Type_ChannelConfig *Channel, Type_RMS *RMS_AmpMon)
{
    double AmpMonitorCurrent;

    if (Channel->OutputSwitch == ON)
    {
        // STEP 1: Calculate the mean of the Current Monitor
        double MeanCurrentCount = (double)FIFO_AmpMon->Sum / FIFO_AmpMon->Depth;
        double MeanDiffVolt = ((MeanCurrentCount * LSB_12BIT_VALUE * System_ADC_Reference) - (Channel->Measure.ZeroCurrentVoltage)) / (AMP_MONITOR_GAIN);
        Channel->Measure.MeanCurrent = MeanDiffVolt / AMP_SENSE_RESISTOR;

        // STEP 2: Calculate the instantaneous current
        double AmpMonitorDiffVolt = ((ADC_AmpMonitorCount * LSB_12BIT_VALUE * System_ADC_Reference) - Channel->Measure.ZeroCurrentVoltage) / AMP_MONITOR_GAIN;
        AmpMonitorCurrent = AmpMonitorDiffVolt / AMP_SENSE_RESISTOR;
    }
    else
    {
        Channel->Measure.MeanCurrent = 0;
        Channel->Measure.RMS_Current = 0;
        return;
    }

    // STEP 3: Update Min Max current or reset min if so desired
    if (Channel->Measure.ResetCurrentMinMax)
    {
        Channel->Measure.MinCurrent = Channel->Measure.MeanCurrent;
        Channel->Measure.MaxCurrent = Channel->Measure.MeanCurrent;
        Channel->Measure.ResetCurrentMinMax = false;
    }
    else
    {
        if (AmpMonitorCurrent < Channel->Measure.MinCurrent)
            Channel->Measure.MinCurrent = AmpMonitorCurrent;
        if (AmpMonitorCurrent > Channel->Measure.MaxCurrent)
            Channel->Measure.MaxCurrent = AmpMonitorCurrent;
    }

    // STEP 4: Calculate the RMS current
    Channel->Measure.RMS_Current = Channel->Measure.RMS_CurrentFunction(RMS_AmpMon, AmpMonitorCurrent);
    if (Channel->Measure.RMS_Current < RMS_TO_MEAN_THREHOLD)
        Channel->Measure.RMS_Current = fabs(Channel->Measure.MeanCurrent);

} // END OF calculateChannelCurrent



/********************************************************************************************************
* @brief Calculates the CHANNEL mean, max, min and RMS voltage.  See notes on function calculateChannelCurrent
*
* @author original: Hab Collector \n
*
* @note: SYSTEM refers to quantities that impact the entire device - CHANNEL impacts on CH1 or CH2
*
* @param ADC_VoltMonitorCount: ADC Count from ADC channel for the specific voltage monitor
* @param FIFO_VoltMon: FIFO structure associated with the specific Volt Monitor channel
* @param Channel: ArbPwrBooster current measure struct associated with the specific channel
* @param RMS_VoltMon: Associated RMS structure
*
* STEP 1: Calculate the mean of the Voltage Monitor
* STEP 2: Calculate the instantaneous voltage
* STEP 3: Update Min Max voltage or reset min if so desired
* STEP 4: Calculate the RMS voltage
********************************************************************************************************/
static void calculateChannelVoltage(double ADC_VoltMonitorCount, Type_16b_FIFO *FIFO_VoltMon, Type_ChannelConfig *Channel, Type_RMS *RMS_VoltMon)
{
    // STEP 1: Calculate the mean of the Voltage Monitor
    double MeanVoltageCount = (double)FIFO_VoltMon->Sum / FIFO_VoltMon->Depth;
    Channel->Measure.MeanVoltage = MeanVoltageCount * LSB_12BIT_VALUE * System_ADC_Reference * VOLT_MON_DIVIDER;

    // STEP 2: Calculate the instantaneous voltage
    double VoltMonitorVoltage = ADC_VoltMonitorCount * LSB_12BIT_VALUE * System_ADC_Reference * VOLT_MON_DIVIDER;

    // STEP 3: Update Min Max voltage or reset min if so desired
#ifdef CAL_MIN_MAX_VOLTAGE
    if (Channel->Measure.ResetVoltageMinMax)
    {
        Channel->Measure.MinVoltage = Channel->Measure.MeanVoltage;
        Channel->Measure.MaxVoltage = Channel->Measure.MeanVoltage;
        Channel->Measure.ResetVoltageMinMax = false;
    }
    else
    {
        if (VoltMonitorVoltage < Channel->Measure.MinVoltage)
            Channel->Measure.MinVoltage = VoltMonitorVoltage;
        if (VoltMonitorVoltage > Channel->Measure.MaxVoltage)
            Channel->Measure.MaxVoltage = VoltMonitorVoltage;
    }
#endif

    // STEP 4: Calculate the RMS voltage
    Channel->Measure.RMS_Voltage = Channel->Measure.RMS_VoltageFunction(RMS_VoltMon, VoltMonitorVoltage);

} // END OF calculateChannelVoltage



/********************************************************************************************************
* @brief Pre-actions to be performed before monitorTaskActions - These actions are performed only once.
*
* @author original: Hab Collector \n
*
********************************************************************************************************/
void monitorTaskInit(void)
{
    DO_NOTHING();

} // END OF monitorTaskInit



/********************************************************************************************************
* @brief Task monitors and controls device actions for error conditions in VS System Supply rails, over temperature,
* out of tolerance 3V3, PID control of Constant Current operation for channel 1 and 2 and Fan 1 and 2 control.
*
* @author original: Hab Collector \n
*
* @note This is where PID control occurs
*
* STEP 1: Do nothing until introduction splash screen completed
* STEP 2: Do nothing if a system error has occurred
* STEP 3: Check System VS supply rail and temperature for errors
* STEP 4: Turn on Channel 1 fan based on power dissipated - turn off after power level drops consistently for 30s
* STEP 5: Check for current limit CH 1 - Constant Current Mode
* STEP 6: Turn on Channel 2 fan based on power dissipated - turn off after power level drops consistently for 30s
* STEP 7: Check for current limit CH 2 - Constant Current Mode
* STEP 8: Make task inactive for a period of time
********************************************************************************************************/
void monitorTaskActions(void)
{
    static bool CriticalSystemError = false;
    static uint8_t LastPotValue = MCP45HVX1_POT_FULL_RESOLUTION;

    // STEP 1: Do nothing until introduction splash screen completed
    if (!ArbPwrBooster.Ready)
        return;

    // STEP 2: Do nothing if a system error has occurred
    if (CriticalSystemError)
        return;

    // STEP 3: Check System VS supply rail and temperature for errors
    char NotUsedStatusMsg[25] = {0x00};
    uint8_t ConfigError = 0;
    systemMeasureWithinLimits(NotUsedStatusMsg, &ConfigError);
    // System VS rails not within limits but not worthy of shutdown - disable input
    if ((ConfigError & CONFIG_POS_VS_ERROR) || (ConfigError & CONFIG_NEG_VS_ERROR))
    {
        CH1_INPUT_DISABLE();
        CH2_INPUT_DISABLE();
    }
    else
    {
        CH1_INPUT_ENABLE();
        CH2_INPUT_ENABLE();
    }
    // System VS rails are critically OV - device damage may occur
    if (ConfigError & CONFIG_VS_CRITICAL_ERROR)
    {
        CriticalSystemError = true;
        MAIN_PWR_OFF();
        printBrightRed("\r\nERROR: Critical on VS supply rail\r\n");
        printBrightRed("Correct supply rail then reset\r\n");
    }
    // System temperature over the limit - device damage may occur
    if (ConfigError & CONFIG_TEMP_ERROR)
    {
        CriticalSystemError = true;
        MAIN_PWR_OFF();
        printBrightRed("\r\nERROR: Critical over temperature\r\n");
        printBrightRed("Cool device then reset\r\n");
    }

    // CHANNEL 1 MONITOR AND CONTROL
    // STEP 4: Turn on Channel 1 fan based on power dissipated - turn off after power level drops consistently for 30s
    double PowerDisipated_OPA549 = (NOMINAL_SUPPLY_RAIL_V - (ArbPwrBooster.CH1.Measure.RMS_Voltage * ArbPwrBooster.CH1.PID->PotStep / ArbPwrBooster.CH1.PID->MaxStepValue)) * ArbPwrBooster.CH1.Measure.RMS_Current;
    if ((ArbPwrBooster.CH1.OutputSwitch == ON) && (!ArbPwrBooster.CH1.Fan.Enable) && (PowerDisipated_OPA549 >= MAX_PD_WITHOUT_HEATSINK))
    {
        ArbPwrBooster.CH1.Fan.Enable = true;
        ArbPwrBooster.CH1.Fan.FanOnDownCounter = FAN_ON_COUNTER_30S;
        CH1_FAN_ENABLE();
    }
    if (ArbPwrBooster.CH1.Fan.Enable)
    {
        if (PowerDisipated_OPA549 < MAX_PD_WITHOUT_HEATSINK)
        {
            ArbPwrBooster.CH1.Fan.FanOnDownCounter--;
            if (ArbPwrBooster.CH1.Fan.FanOnDownCounter == 0)
            {
                ArbPwrBooster.CH1.Fan.Enable = false;
                CH1_FAN_DISABLE();
            }
        }
        else
        {
            ArbPwrBooster.CH1.Fan.FanOnDownCounter = FAN_ON_COUNTER_30S;
        }
    }

    // STEP 5: Check for current limit CH 1 - Constant Current Mode
    if ((ArbPwrBooster.CH1.OutputSwitch == ON) && (ArbPwrBooster.CH1.Limit.Enable))
    {
#ifdef PRINT_CC_PID_UPDATES
        static uint16_t TickCount = 0;
        static uint16_t DataUpdateCount = 0;
        static bool PrintColumnHeader = true;
        TickCount++;
#endif
        if (PID_updateDigitalPot(ArbPwrBooster.CH1.PID, ArbPwrBooster.CH1.Measure.RMS_Current, ArbPwrBooster.CH1.Limit.Current, (MONITOR_UPDATE_RATE * 1E-3)) == PID_UPDATE)
        {
            if (LastPotValue != ArbPwrBooster.CH1.PID->PotStep)
            {
                MCP45HVX1_WriteWiperVerify(&hi2c1, A1A0_EXTERNAL_ADDR_CH1, ArbPwrBooster.CH1.PID->PotStep);
                LastPotValue = ArbPwrBooster.CH1.PID->PotStep;
#ifdef PRINT_CC_PID_UPDATES
                if (PrintColumnHeader)
                {
                    printf("\r\n\n#\tTick\tStep\tIrms\r\n");
                    fflush(stdout);
                    PrintColumnHeader = false;
                }
                DataUpdateCount++;
                 char PrintMsg[100];
                sprintf(PrintMsg, "%d\t%d\t%d\t%2.3f\r\n", DataUpdateCount, TickCount, ArbPwrBooster.CH1.PID->PotStep, ArbPwrBooster.CH1.Measure.RMS_Current);
                printGreen(PrintMsg);
#endif
            }
        }
    }
    else
    {
#ifdef PRINT_CC_PID_UPDATES
        TickCount = 0;
        DataUpdateCount = 0;
        PrintColumnHeader = true;
#endif
    }

    // CHANNEL 2 MONITOR AND CONTROL
    // STEP 6: Turn on Channel 2 fan based on power dissipated - turn off after power level drops consistently for 30s
    PowerDisipated_OPA549 = (NOMINAL_SUPPLY_RAIL_V - (ArbPwrBooster.CH2.Measure.RMS_Voltage * ArbPwrBooster.CH2.PID->PotStep / ArbPwrBooster.CH2.PID->MaxStepValue)) * ArbPwrBooster.CH2.Measure.RMS_Current;
    if ((ArbPwrBooster.CH2.OutputSwitch == ON) && (!ArbPwrBooster.CH2.Fan.Enable) && (PowerDisipated_OPA549 >= MAX_PD_WITHOUT_HEATSINK))
    {
        ArbPwrBooster.CH2.Fan.Enable = true;
        ArbPwrBooster.CH2.Fan.FanOnDownCounter = FAN_ON_COUNTER_30S;
        CH2_FAN_ENABLE();
    }
    if (ArbPwrBooster.CH2.Fan.Enable)
    {
        if (PowerDisipated_OPA549 < MAX_PD_WITHOUT_HEATSINK)
        {
            ArbPwrBooster.CH2.Fan.FanOnDownCounter--;
            if (ArbPwrBooster.CH2.Fan.FanOnDownCounter == 0)
            {
                ArbPwrBooster.CH2.Fan.Enable = false;
                CH2_FAN_DISABLE();
            }
        }
        else
        {
            ArbPwrBooster.CH2.Fan.FanOnDownCounter = FAN_ON_COUNTER_30S;
        }
    }

    // STEP 7: Check for current limit CH 2 - Constant Current Mode
    if ((ArbPwrBooster.CH2.OutputSwitch == ON) && (ArbPwrBooster.CH2.Limit.Enable))
    {
        if (PID_updateDigitalPot(ArbPwrBooster.CH2.PID, ArbPwrBooster.CH2.Measure.RMS_Current, ArbPwrBooster.CH2.Limit.Current, (MONITOR_UPDATE_RATE * 1E-3)) == PID_UPDATE)
        {
            if (LastPotValue != ArbPwrBooster.CH2.PID->PotStep)
            {
                MCP45HVX1_WriteWiperVerify(&hi2c1, A1A0_EXTERNAL_ADDR_CH2, ArbPwrBooster.CH2.PID->PotStep);
                LastPotValue = ArbPwrBooster.CH2.PID->PotStep;
            }
        }
    }

    // STEP 8: Make task inactive for a period of time
    osDelay(MONITOR_UPDATE_RATE);

} // END OF monitorTaskActions



/********************************************************************************************************
* @brief ADC1 is configured for DMA single shot conversion mode.  At the end of each conversion the ADC must
* be restarted for the next conversion.  Issue this command to start a conversion.  When the conversion is
* completed the results will be handled in HAL_ADC_ConvCpltCallback().  As this is single shot, you must call
* this function at the end of conversion if you want another conversion - and so on and so on.
*
* @author original: Hab Collector \n
*
* STEP 1: Start ADC 1 conversion all channels in single shot DMA mode
********************************************************************************************************/
void ADC1_StartConversion(void)
{
    // STEP 1: Start ADC 1 conversion all channels in single shot DMA mode
    HAL_ADC_Start_DMA(&hadc1, (uint32_t *)ADC1_CountValue, ADC1_NUMBER_OF_CHANNELS);

}  // END OF ADC1_StartConversion



/********************************************************************************************************
* @brief Checks the system values of +VS, -VS, Temperature and Vref to see if they are within the specified
* limits of operation.  All errors are OR together to the error variable, but only the first error description
* is returned.
*
* @author original: Hab Collector \n
*
* @note: SYSTEM refers to quantities that impact the entire device - CHANNEL impacts on CH1 or CH2
*
* @param ErrorDescription: Returned by reference a description of the error
* @param ErrorNumber: Returned by reference the error number
*
* @return True if no config errror found otherwise returns false
*
* STEP 1: Check System +VS within operation limits
* STEP 2: Check System -VS within operation limits
* STEP 3: Check for a fault critical VS supply OV condition - device damage may occur
* STEP 4: Check System Vref
* STEP 5: Check System Temperature
* STEP 6: For no error
********************************************************************************************************/
bool systemMeasureWithinLimits(char *ErrorDescription, uint8_t *ErrorNumber)
{
    bool FirstErrorFound = false;
    *ErrorNumber = CONFIG_NO_ERROR;

    // STEP 1: Check System +VS within operation limits
    if ((ArbPwrBooster.SystemMeasure.Positive_VS > SYSTEM_POS_VS_HIGH) || (ArbPwrBooster.SystemMeasure.Positive_VS < SYSTEM_POS_VS_LOW))
    {
        *ErrorNumber |= (1 << CONFIG_POS_VS_LIMIT_MASK);
        if (!FirstErrorFound)
        {
            sprintf(ErrorDescription, "+VS: %3.1fV to %3.1fV", SYSTEM_POS_VS_LOW, SYSTEM_POS_VS_HIGH);
            FirstErrorFound = true;
        }
    }

    // STEP 2: Check System -VS within operation limits
    if ((ArbPwrBooster.SystemMeasure.Negative_VS > SYSTEM_NEG_VS_HIGH) || (ArbPwrBooster.SystemMeasure.Negative_VS < SYSTEM_NEG_VS_LOW))
    {
        *ErrorNumber |= (uint8_t)(1 << CONFIG_NEG_VS_LIMIT_MASK);
        if (!FirstErrorFound)
        {
            sprintf(ErrorDescription, "-VS: %3.1fV to %3.1fV", SYSTEM_NEG_VS_LOW, SYSTEM_NEG_VS_HIGH);
            FirstErrorFound = true;
        }
    }

    // STEP 3: Check for a fault critical VS supply OV condition - device damage may occur
    if ((ArbPwrBooster.SystemMeasure.Positive_VS >= SYSTEM_POS_VS_LIMIT) || (ArbPwrBooster.SystemMeasure.Negative_VS <= SYSTEM_NEG_VS_LIMIT))
    {
        *ErrorNumber |= (uint8_t)(1 << CONFIG_VS_CRITICAL_ERROR_MASK);
    }

    // STEP 4: Check System Vref
    if ((ArbPwrBooster.SystemMeasure.VDD_VDREF > SYSTEM_3V3_UPPER_LIMIT) || (ArbPwrBooster.SystemMeasure.VDD_VDREF < SYSTEM_3V3_LOWER_LIMIT))
    {
        *ErrorNumber |= (uint8_t)(1 << CONFIG_VREF_MASK);
        if (!FirstErrorFound)
        {
            sprintf(ErrorDescription, "VREF: %4.3fV to %4.3fV", SYSTEM_3V3_LOWER_LIMIT, SYSTEM_3V3_UPPER_LIMIT);
            FirstErrorFound = true;
        }
    }

    // STEP 5: Check System Temperature
    if (ArbPwrBooster.SystemMeasure.TempDegreeC >= SYSTEM_TEMP_UPPER_LIMIT)
    {
        *ErrorNumber |= (uint8_t)(1 << CONFIG_TEMP_MASK);
        if (!FirstErrorFound)
        {
            sprintf(ErrorDescription, "%dC < Temp < %dC", SYSTEM_TEMP_LOWER_LIMIT, SYSTEM_TEMP_UPPER_LIMIT);
            FirstErrorFound = true;
        }
    }

    // STEP 6: For no error
    if (*ErrorNumber == CONFIG_NO_ERROR)
    {
        sprintf(ErrorDescription, "I'm good how about you.");
        return(true);
    }
    else
    {
        return(false);
    }

} // END OF systemMeasureWithinLimits



/********************************************************************************************************
* @brief When no current flows through the sense resistor the actual measured current should be zero Amps.
* This value in volts should be the current shunt monitor IC reference voltage.  The reference voltage is 1/2
* 3.3V (VREF) = 1.650V.  To account for inaccuracies in the system this function should be called when the
* output is disconnected (no current flowing) to establish the true reference for 0 Amp current flow.
*
* @author original: Hab Collector \n
*
* @note: ***This function should only be called when the channel output is switched off - no current flow
* @note: If called when the output is switched on the default value (1.650V) is used with a false return
*
* @param Channel: Should be CHANNEL_1 or CHANNEL_2
*
* @return True with the ArbPwrBooster struct member ZeroCurrentVoltage set to the value when output is off
*
* STEP 1: CH 1: Set the zero offset voltage (the present mean value) if channel is switched off
* STEP 2: CH 2: Set the zero offset voltage (the present mean value) if channel is switched off
********************************************************************************************************/
bool updateAmpMonitorZeroVoltage(Type_Channel Channel)
{
    if (Channel == CHANNEL_1)
    {
        // STEP 1: CH 1: Set the zero offset voltage (the present mean value) if channel is switched off
        if (ArbPwrBooster.CH1.OutputSwitch == OFF)
        {
            double MeanCount_ADC = (double)FIFO_CH1_AmpMon->Sum / FIFO_CH1_AmpMon->Depth;
            ArbPwrBooster.CH1.Measure.ZeroCurrentVoltage = MeanCount_ADC * LSB_12BIT_VALUE * System_ADC_Reference;
            return(true);
        }
        else
        {
            ArbPwrBooster.CH1.Measure.ZeroCurrentVoltage = CURRENT_MON_ZERO_OFFSET;
            return(false);
        }
    }
    else
    {
        // STEP 2: CH 2: Set the zero offset voltage (the present mean value) if channel is switched off
        if (ArbPwrBooster.CH2.OutputSwitch == OFF)
        {
            double MeanCount_ADC = (double)FIFO_CH2_AmpMon->Sum / FIFO_CH2_AmpMon->Depth;
            ArbPwrBooster.CH2.Measure.ZeroCurrentVoltage = MeanCount_ADC * LSB_12BIT_VALUE * System_ADC_Reference;
            return(true);
        }
        else
        {
            ArbPwrBooster.CH2.Measure.ZeroCurrentVoltage = CURRENT_MON_ZERO_OFFSET;
            return(false);
        }
    }

} // END OF updateAmpMonitorZeroVoltage
