habworks/Arb_Power_Booster/Firmware/ArbPwrBooster_App/TouchGFX/gui/src/screen_splash_screen/Screen_SplashPresenter.cpp

#include <gui/screen_splash_screen/Screen_SplashView.hpp>
#include <gui/screen_splash_screen/Screen_SplashPresenter.hpp>

Screen_SplashPresenter::Screen_SplashPresenter(Screen_SplashView& v)
    : view(v)
{

}

void Screen_SplashPresenter::activate()
{

}

void Screen_SplashPresenter::deactivate()
{

}
